LorcaSnep/Lorca-Throttle/Images/Lorca Throttle V3.2 Back.PNG

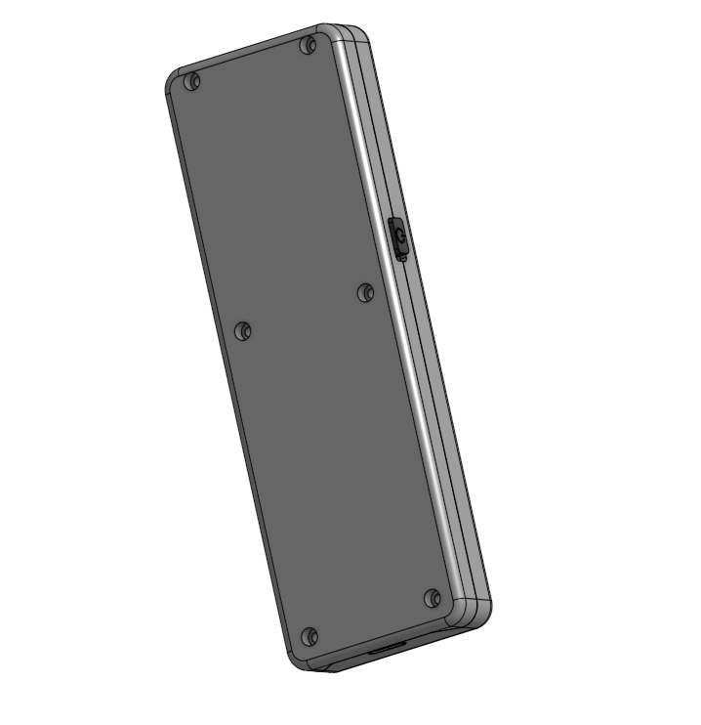
Images/Lorca Throttle V3.2 Back.PNG
