LorcaSnep/Lorca-Throttle/Images/Lorca Throttle V3.2 Bottom.PNG

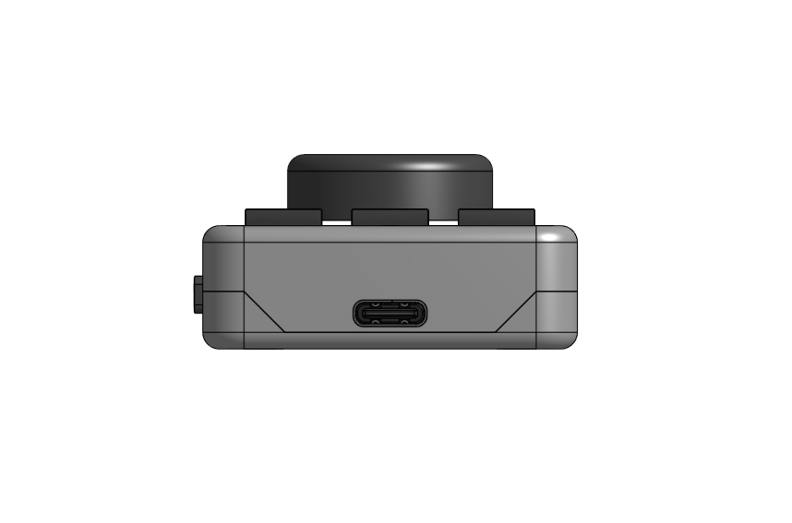
Images/Lorca Throttle V3.2 Bottom.PNG
