LorcaSnep/Lorca-Throttle/Images/Lorca Throttle V3.2 KP Back.PNG

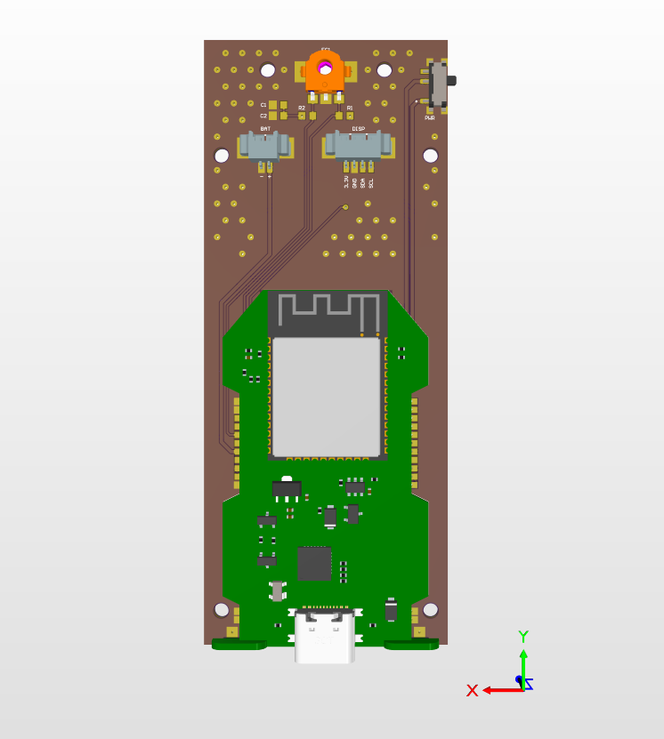
Images/Lorca Throttle V3.2 KP Back.PNG
