LorcaSnep/Lorca-Throttle/Images/Lorca Throttle V3.2 Module Front.PNG

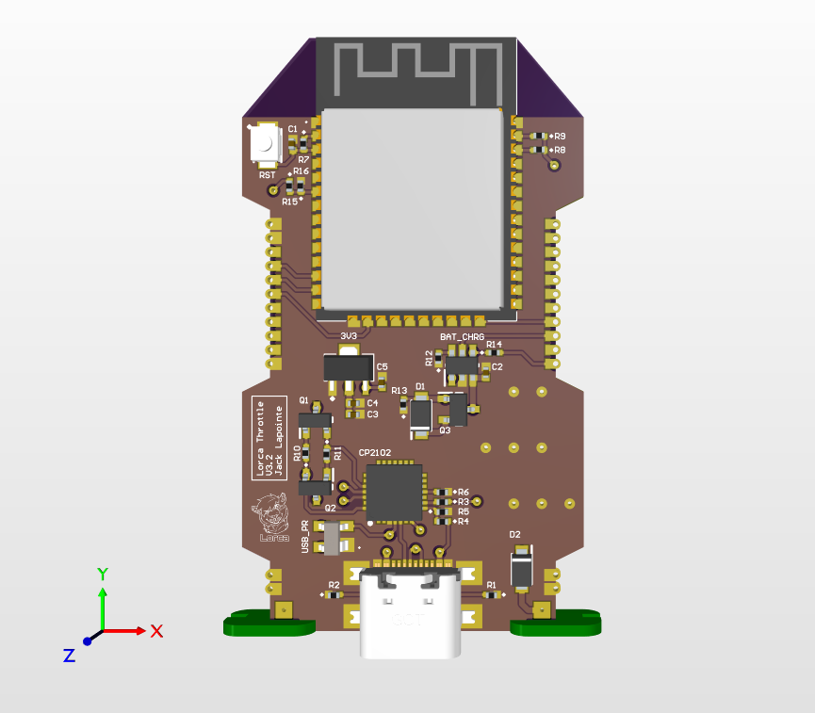
Images/Lorca Throttle V3.2 Module Front.PNG
