LorcaSnep/Lorca-Throttle/Images/Lorca Throttle V4.0 Back.PNG

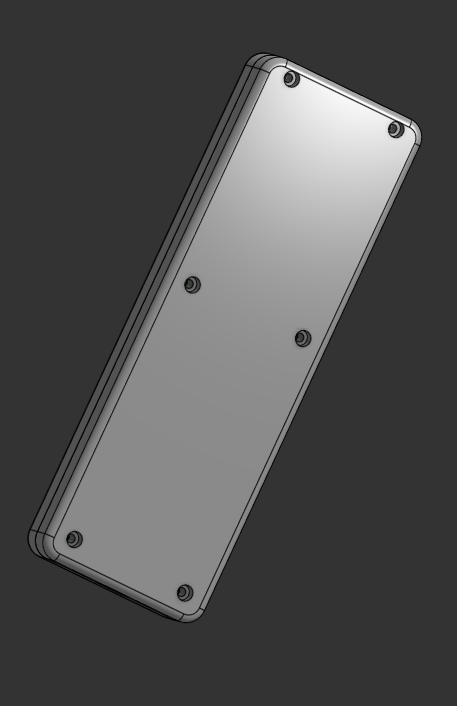
Images/Lorca Throttle V4.0 Back.PNG
