LorcaSnep/Lorca-Throttle/Images/Lorca Throttle V4.0 PCB Back.PNG

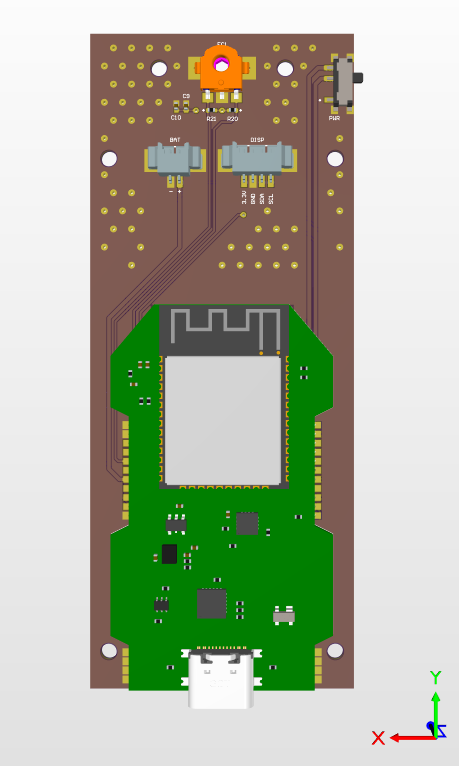
Images/Lorca Throttle V4.0 PCB Back.PNG
