LorcaSnep/Lorca-Throttle/Images/Lorca Throttle V4.0 PCB Front.PNG

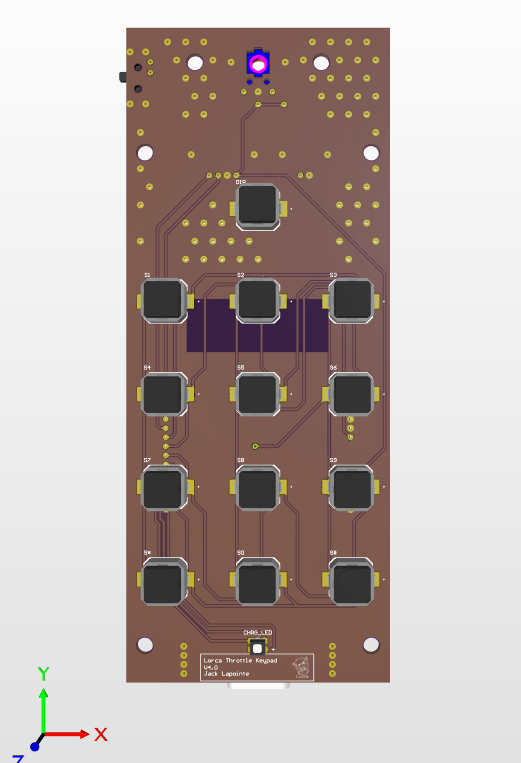
Images/Lorca Throttle V4.0 PCB Front.PNG
