LorcaSnep/Lorca-Throttle/Case Hardware/Keys/Star Key.step

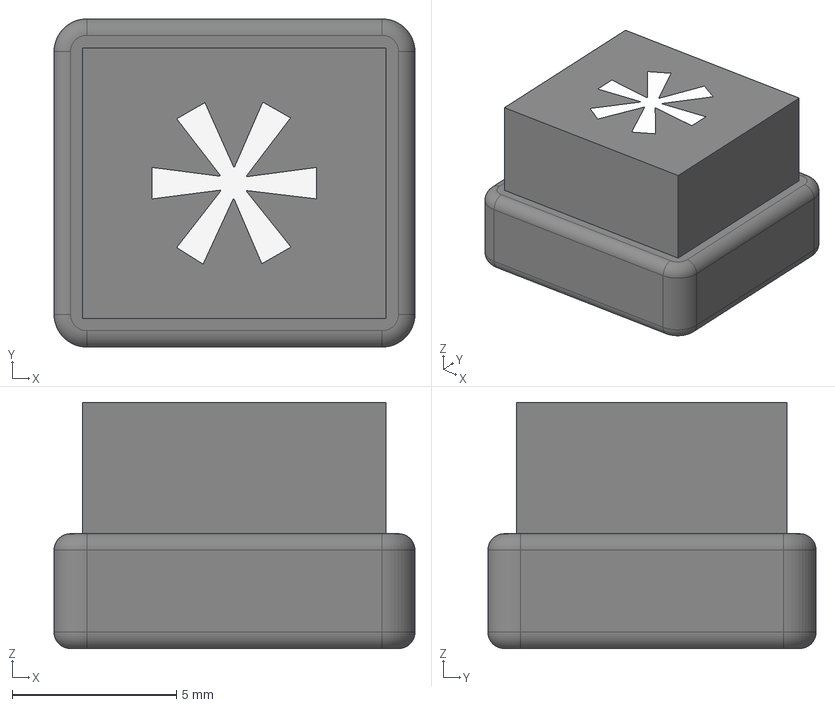
[picture p29: CAD file, 2026-03-01]
Case Hardware/Keys/Star Key.step
11.0 x 10.0 x 7.50 mm
