LorcaSnep/Lorca-Throttle/Case Hardware/LED Insert.stl

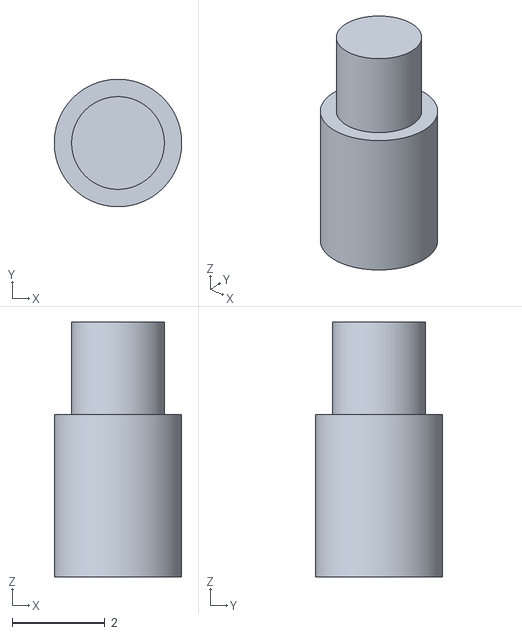
[picture p30: CAD file, 2025-09-22]
Case Hardware/LED Insert.stl
2.75 x 2.75 x 5.50
