LorcaSnep/Lorca-Throttle/Case Hardware/Keys/Num Key.stl

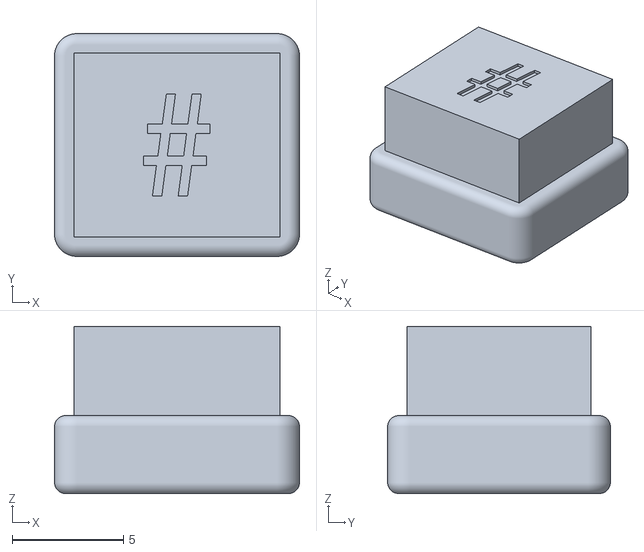
[picture p31: CAD file, 2025-10-13]
Case Hardware/Keys/Num Key.stl
11.0 x 10.0 x 7.50
