LorcaSnep/Lorca-Throttle/Case Hardware/Keys/- Key.stl

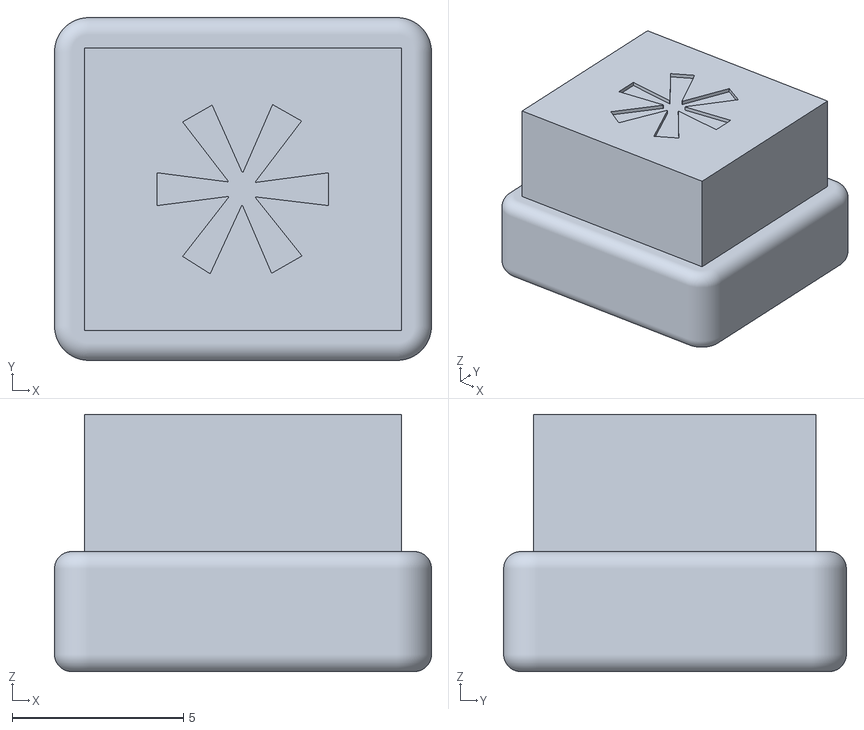
[picture p32: CAD file, 2025-10-13]
Case Hardware/Keys/- Key.stl
11.0 x 10.0 x 7.50
