LorcaSnep/Lorca-Throttle/Case Hardware/Throttle Knob Fastener.stl

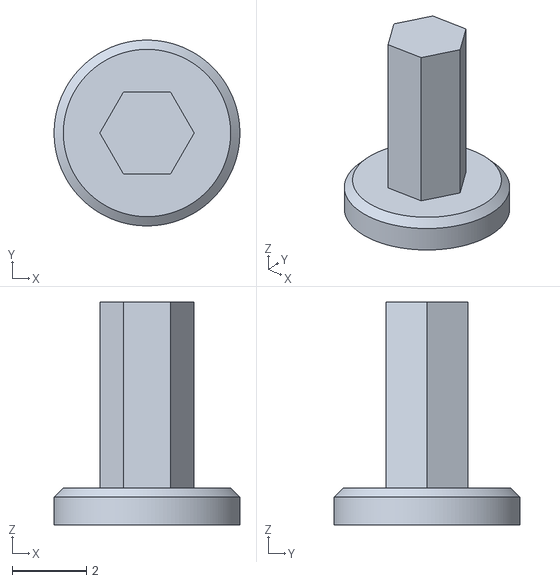
[picture p33: CAD file, 2025-09-22]
Case Hardware/Throttle Knob Fastener.stl
5.00 x 5.00 x 6.00
